bradparks/DrawingRobot/OpenSCAD/pezzi/ballcaster/ball caster pololu 955 misure1.jpg

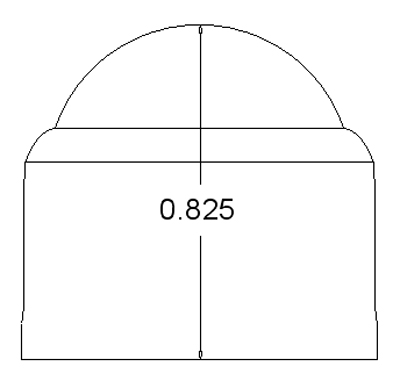
OpenSCAD/pezzi/ballcaster/ball caster pololu 955 misure1.jpg
